a6-a9-ai/Smart_chicken_coop/PCB_footprints/2450AT18A100E.step

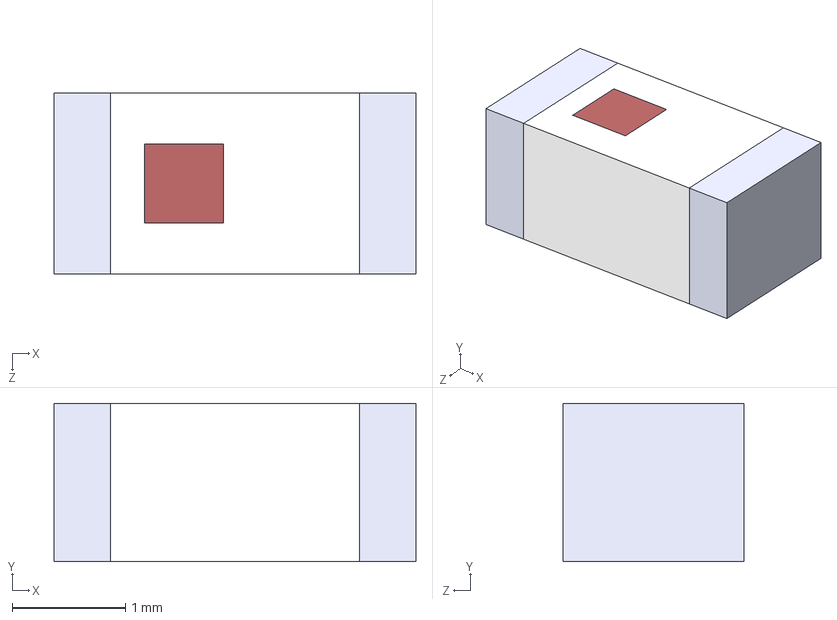
[picture p22: CAD file, 2025-11-14]
PCB_footprints/2450AT18A100E.step
3.20 x 1.40 x 1.60 mm
