a6-a9-ai/Smart_chicken_coop/PCB_footprints/FTSH-105-01-F-DV-P-TR.step

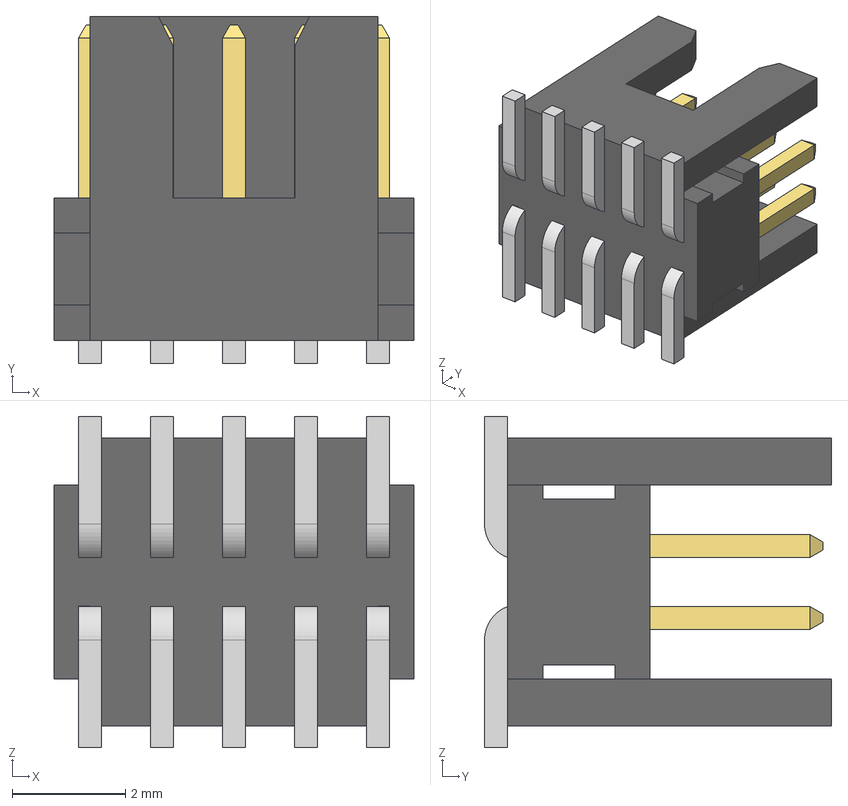
[picture p23: CAD file, 2025-11-14]
PCB_footprints/FTSH-105-01-F-DV-P-TR.step
6.35 x 6.12 x 5.84 mm
FTSH-105-01-F-DV-K_body
FTSH-105-01-F-DV-K_pins1
FTSH-105-01-F-DV-K_pins2
