a6-a9-ai/Smart_chicken_coop/PCB_footprints/SMD-DIODE-SCHOTTKY-40V-1A_DO-214AC_.step

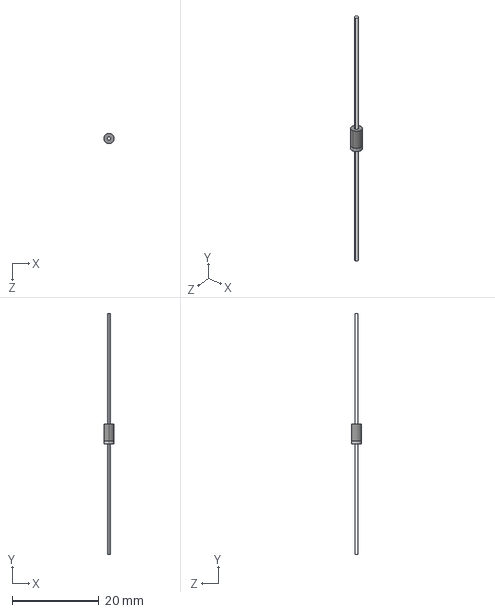
[picture p24: CAD file, 2025-11-14]
PCB_footprints/SMD-DIODE-SCHOTTKY-40V-1A_DO-214AC_.step
2.35 x 55.4 x 2.35 mm
