a6-a9-ai/Smart_chicken_coop/PCB_footprints/MCP1640T-I_CHY.step

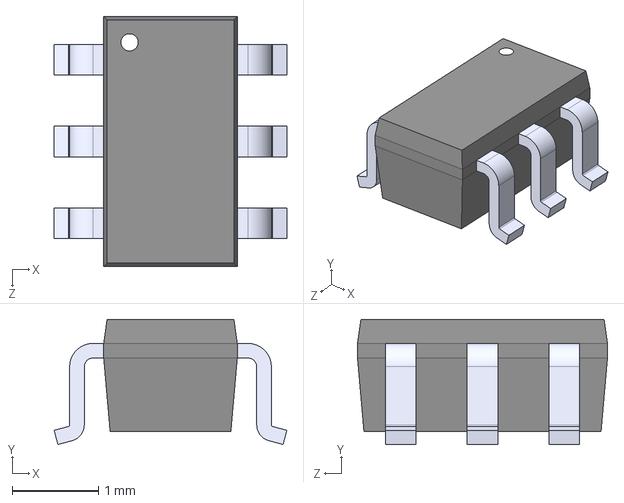
[picture p25: CAD file, 2025-11-14]
PCB_footprints/MCP1640T-I_CHY.step
2.70 x 1.45 x 2.90 mm
