a6-a9-ai/Smart_chicken_coop/PCB_footprints/BQ2000PN-B5.step

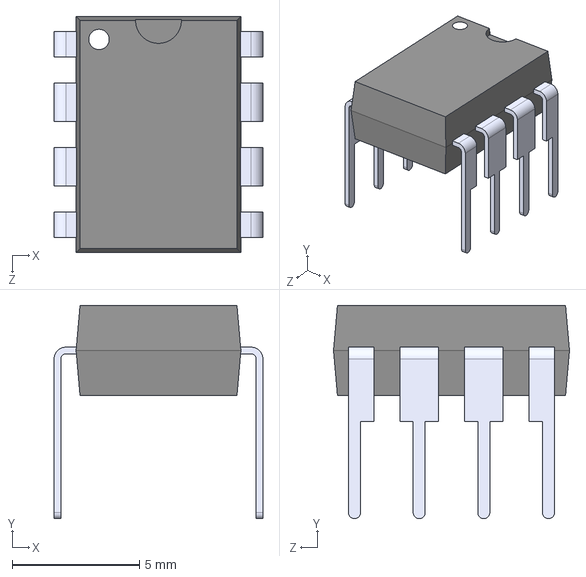
[picture p26: CAD file, 2025-11-14]
PCB_footprints/BQ2000PN-B5.step
8.21 x 8.38 x 9.27 mm
