a6-a9-ai/Smart_chicken_coop/PCB_footprints/CMC-4015-40P.step

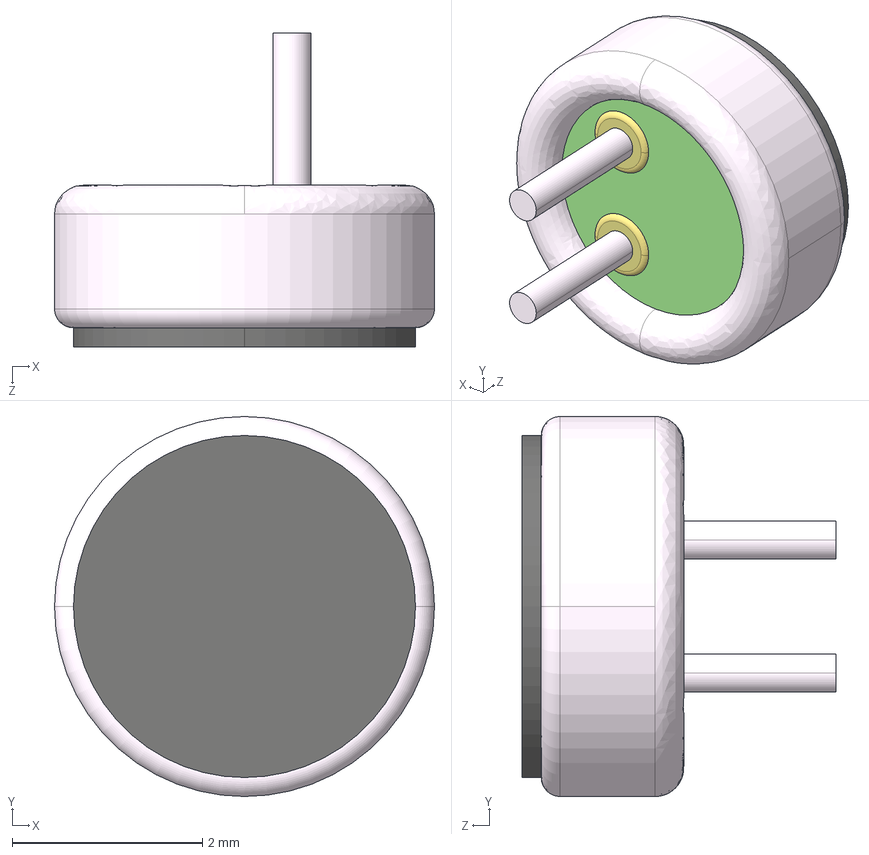
[picture p27: CAD file, 2025-11-14]
PCB_footprints/CMC-4015-40P.step
4.00 x 4.00 x 3.30 mm
