a6-a9-ai/Smart_chicken_coop/PCB_footprints/MCP602-I_P.step

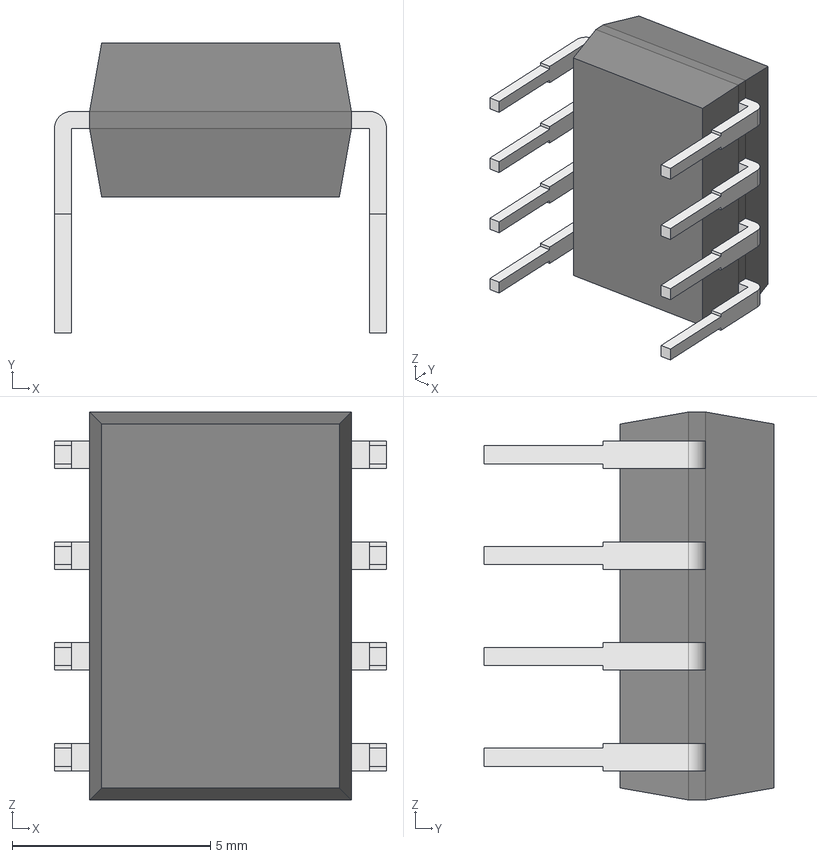
[picture p28: CAD file, 2025-11-14]
PCB_footprints/MCP602-I_P.step
8.37 x 7.32 x 9.78 mm
Body001 (Mirror #1) x 5
