a6-a9-ai/Smart_chicken_coop/PCB_footprints/LM317TG.step

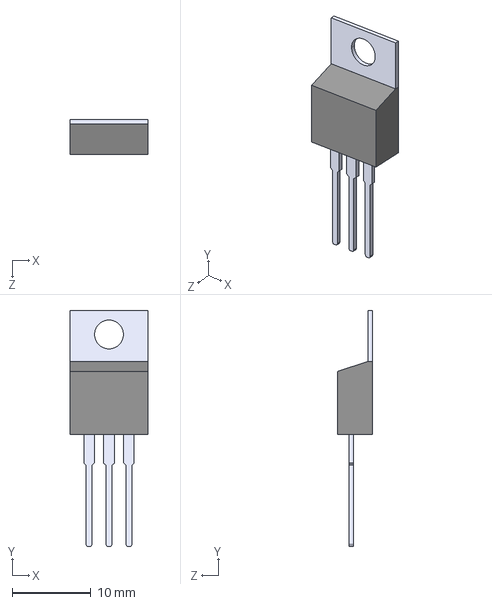
[picture p29: CAD file, 2025-11-14]
PCB_footprints/LM317TG.step
9.97 x 30.0 x 4.44 mm
