a6-a9-ai/Smart_chicken_coop/PCB_footprints/RFM95W-915S2.step

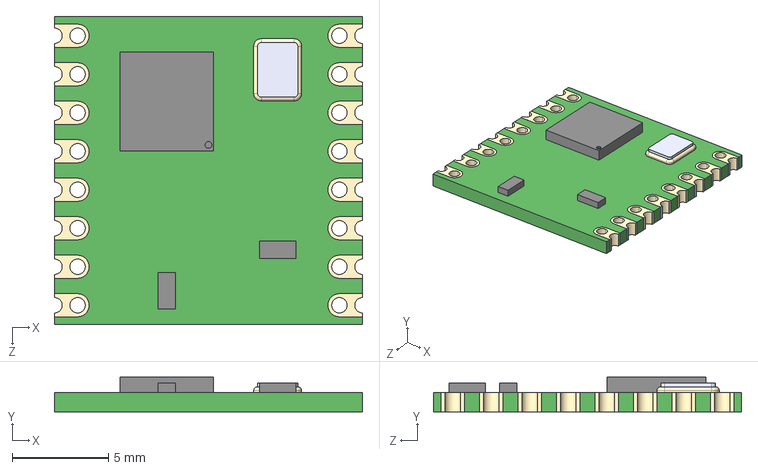
[picture p30: CAD file, 2025-11-14]
PCB_footprints/RFM95W-915S2.step
16.0 x 1.80 x 16.0 mm
