a6-a9-ai/Smart_chicken_coop/PCB_footprints/22-28-4030.step

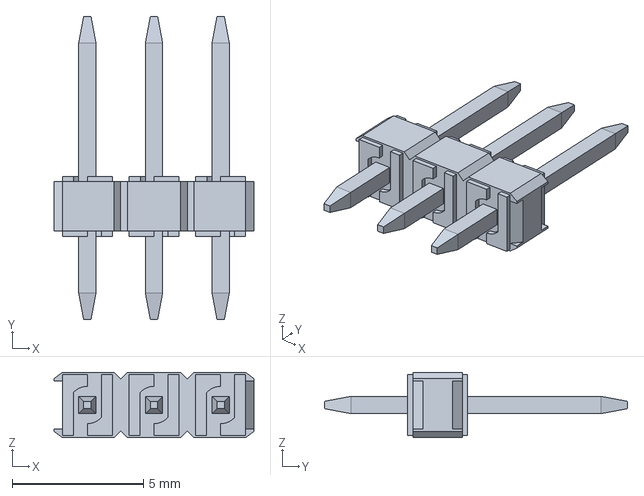
[picture p31: CAD file, 2025-11-14]
PCB_footprints/22-28-4030.step
7.62 x 11.6 x 2.49 mm
