a6-a9-ai/Smart_chicken_coop/PCB_footprints/LM317T.step

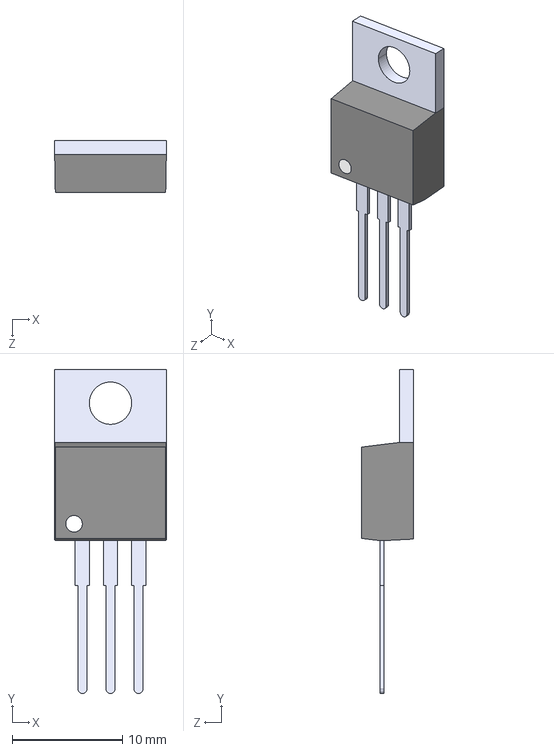
[picture p32: CAD file, 2025-11-14]
PCB_footprints/LM317T.step
10.2 x 29.3 x 4.70 mm
