a6-a9-ai/Smart_chicken_coop/PCB_footprints/DHT11.step

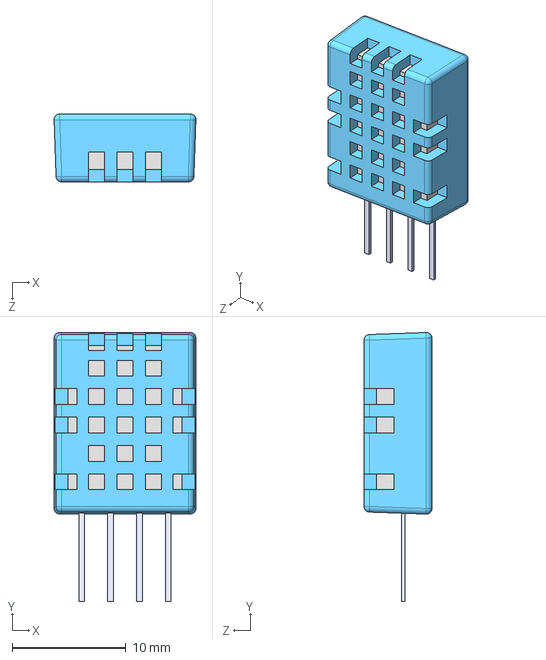
[picture p33: CAD file, 2025-11-14]
PCB_footprints/DHT11.step
12.5 x 23.7 x 6.00 mm
