a6-a9-ai/Smart_chicken_coop/PCB_footprints/LM317T_LF01.step

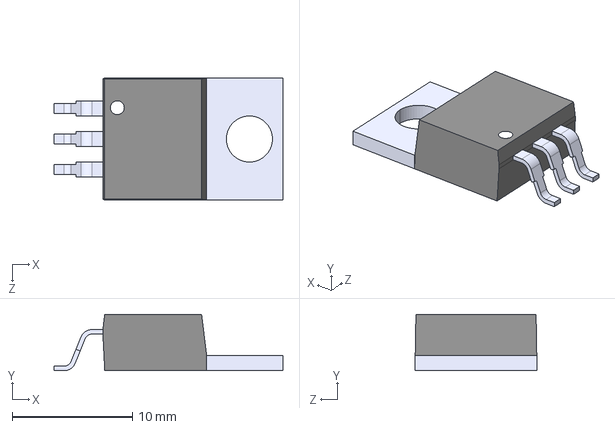
[picture p34: CAD file, 2025-11-14]
PCB_footprints/LM317T_LF01.step
19.1 x 4.70 x 10.2 mm
