a6-a9-ai/Smart_chicken_coop/PCB_footprints/B2B-PH-K-S_LF__SN_.step

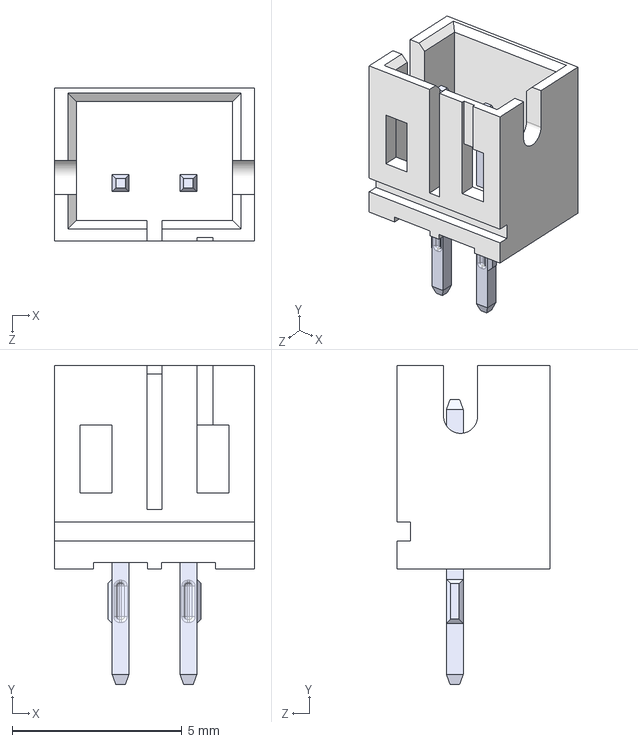
[picture p35: CAD file, 2025-11-14]
PCB_footprints/B2B-PH-K-S_LF__SN_.step
5.90 x 9.40 x 4.50 mm
