a6-a9-ai/Smart_chicken_coop/soft_nRF_R/src/bluetooth.c

#include "bluetooth.h"
#define COMPANY_ID_TEST 0x0D06 

#define LED_0_TRIGGER                DT_ALIAS(led0)
#define LED_1_TRIGGER                DT_ALIAS(led1)
#define LED_2_TRIGGER                DT_ALIAS(led2)

static const struct gpio_dt_spec led0 = GPIO_DT_SPEC_GET(LED_0_TRIGGER, gpios);
static const struct gpio_dt_spec led1 = GPIO_DT_SPEC_GET(LED_1_TRIGGER, gpios);
static const struct gpio_dt_spec led2 = GPIO_DT_SPEC_GET(LED_2_TRIGGER, gpios);



struct ble_mfg_data_t{
    uint16_t company_id;
    uint8_t payload;
} __packed;

static void device_found(const bt_addr_le_t *addr,
                        int8_t rssi,
                        uint8_t type,
                        struct net_buf_simple *ad){

    char addr_str[BT_ADDR_LE_STR_LEN];
    struct ble_mfg_data_t *mfg_data;
    char dev_name[33];

    bt_addr_le_to_str(addr, addr_str, sizeof(addr_str));
    
    memset(dev_name, 0, sizeof(dev_name));
    struct net_buf_simple_state name_state;
    net_buf_simple_save(ad, &name_state);
    
    while (ad->len > 1){
        uint8_t len = net_buf_simple_pull_u8(ad);
        if (len == 0) break;
        if (len > ad->len) break;
        uint8_t type = net_buf_simple_pull_u8(ad);
        if (type == BT_DATA_NAME_COMPLETE || type == BT_DATA_NAME_SHORTENED){
            uint8_t name_len = len - 1;
            if (name_len > 32) name_len = 32;
            memcpy(dev_name, ad->data, name_len);
            dev_name[name_len] = '\0';
            break; 
        }
        net_buf_simple_pull(ad, len - 1);
    }
    net_buf_simple_restore(ad, &name_state);
    if (dev_name[0] == 0){
        strcpy(dev_name, "(Unknown)");
    }

    //printk("[DEVICE] %s (RSSI %d) Name: %s\n", addr_str, rssi, dev_name);

    struct net_buf_simple_state state;
    net_buf_simple_save(ad, &state);

    while (ad->len > 1){
        uint8_t len = net_buf_simple_pull_u8(ad);
        uint8_t ad_type;

        if (len == 0){
            break;
        }
        if (len > ad->len){
            break;
        }

        ad_type = net_buf_simple_pull_u8(ad);
        
        if (strncmp(dev_name, "smartChicken", 12) == 0){
            if ((len +1) == sizeof(struct ble_mfg_data_t)){
                mfg_data = (struct ble_mfg_data_t *)ad->data;
                
                     uint16_t found_company_id = sys_le16_to_cpu(mfg_data->company_id);
                     uint8_t payload = mfg_data->payload;
                     uint8_t temp = (payload >> 0) & 0x01;
                     uint8_t gas  = (payload >> 1) & 0x01;
                     uint8_t attack = (payload >> 2) & 0x01;
                     
                     
                     printk("data:[");
                     for (int i = 0; i < ad->len; i++) {
                         printk("%02X ", ad->data[i]);
                     }
                     printk("]\n");
                     uint8_t last_byte = ad->data[ad->len - 1];
                     printk("  last byte: 0x%02X\n", last_byte);
                     // Control GPIO pin based on bit 1 (gas) using devicetree led0
                     if (gpio_is_ready_dt(&led0)) {
                            if (last_byte == 1) {
                                gpio_pin_set_dt(&led0, 1);
                                printk("LED ON (bit 1 detected)\n");
                                gpio_pin_set_dt(&led1, 0);
                                printk("LED OFF (bit 1 not detected)\n");
                            }
                        }
                    
                     if (gpio_is_ready_dt(&led1)) {
                         if (last_byte == 2) {
                             gpio_pin_set_dt(&led1, 1);
                             printk("LED ON (bit 2 detected)\n");
                             gpio_pin_set_dt(&led0, 0);
                             printk("LED OFF (bit 1 not detected)\n");
                         }
                     }
                     if (gpio_is_ready_dt(&led2)) {
                         if (last_byte == 3) {
                            gpio_pin_set_dt(&led0, 1);
                             printk("LED ON (bit 1 detected)\n");
                             gpio_pin_set_dt(&led1, 1);
                             printk("LED ON (bit 1 detected)\n");
                     }

                }
            }
        }
        net_buf_simple_pull(ad, len - 1);
    }
    net_buf_simple_restore(ad, &state);
}

int scanner_init(void)
{
    struct bt_le_scan_param scan_param = {
        .type       = BT_LE_SCAN_TYPE_PASSIVE,
        .options    = BT_LE_SCAN_OPT_NONE,
        .interval   = 0x0150,
        .window     = 0x0030,
    };
    int err;

    // Initialize GPIO for LED control using devicetree alias led0
    if (!gpio_is_ready_dt(&led0)) {
        printk("Error: LED GPIO device not ready\n");
        return -1;
    }
    if (!gpio_is_ready_dt(&led1)) {
        printk("Error: LED GPIO device not ready\n");
        return -1;
    }
    if (!gpio_is_ready_dt(&led2)) {
        printk("Error: LED GPIO device not ready\n");
        return -1;
    }

    // Configure pin as output
    err = gpio_pin_configure_dt(&led0, GPIO_OUTPUT_INACTIVE);
    err = gpio_pin_configure_dt(&led1, GPIO_OUTPUT_INACTIVE);
    err = gpio_pin_configure_dt(&led2, GPIO_OUTPUT_INACTIVE);
    if (err) {
        printk("Error configuring LED GPIO pin (err %d)\n", err);
        return err;
    }
    printk("LED GPIO initialized via devicetree\n");

    err = bt_enable(NULL);
    if (err){
        printk("Bluetooth init failed (err %d)\n", err);
        return err;
    }

    printk("Bluetooth initialized\n");

    err = bt_le_scan_start(&scan_param, device_found);
    if (err){
        printk("Starting scanning failed (err %d)\n", err);
        return err;
    }

    printk("Scanning successfully started\n");
    return 0;
}
